bbogush/nand_programmer/qt/parallel_chip_db.h

/*  Copyright (C) 2020 NANDO authors
 *  This program is free software; you can redistribute it and/or modify
 *  it under the terms of the GNU General Public License version 3.
 */

#ifndef PARALLEL_CHIP_DB_H
#define PARALLEL_CHIP_DB_H

#include "chip_db.h"
#include "parallel_chip_info.h"

#include <cstdint>
#include <QString>
#include <QObject>
#include <QVector>
#include <QFile>

class ParallelChipDb : public ChipDb
{
private:
    QString dbFileName = "nando_parallel_chip_db.csv";

protected:
    QString getDbFileName() override;
    ChipInfo *stringToChipInfo(const QString &s) override;
    int chipInfoToString(ChipInfo *chipInfo, QString &s) override;

public:
    enum
    {
        CHIP_PARAM_NAME,
        CHIP_PARAM_PAGE_SIZE,
        CHIP_PARAM_BLOCK_SIZE,
        CHIP_PARAM_TOTAL_SIZE,
        CHIP_PARAM_SPARE_SIZE,
        CHIP_PARAM_BB_MARK_OFF,
        CHIP_PARAM_T_CS,
        CHIP_PARAM_T_CLS,
        CHIP_PARAM_T_ALS,
        CHIP_PARAM_T_CLR,
        CHIP_PARAM_T_AR,
        CHIP_PARAM_T_WP,
        CHIP_PARAM_T_RP,
        CHIP_PARAM_T_DS,
        CHIP_PARAM_T_CH,
        CHIP_PARAM_T_CLH,
        CHIP_PARAM_T_ALH,
        CHIP_PARAM_T_WC,
        CHIP_PARAM_T_RC,
        CHIP_PARAM_T_REA,
        CHIP_PARAM_ROW_CYCLES,
        CHIP_PARAM_COL_CYCLES,
        CHIP_PARAM_READ1_CMD,
        CHIP_PARAM_READ2_CMD,
        CHIP_PARAM_READ_SPARE_CMD,
        CHIP_PARAM_READ_ID_CMD,
        CHIP_PARAM_RESET_CMD,
        CHIP_PARAM_WRITE1_CMD,
        CHIP_PARAM_WRITE2_CMD,
        CHIP_PARAM_ERASE1_CMD,
        CHIP_PARAM_ERASE2_CMD,
        CHIP_PARAM_STATUS_CMD,
        CHIP_PARAM_SET_FEATURE_CMD,
        CHIP_PARAM_ENABLE_HW_ECC_ADDR,
        CHIP_PARAM_ENABLE_HW_ECC_VALUE,
        CHIP_PARAM_DISABLE_HW_ECC_VALUE,
        CHIP_PARAM_ID1,
        CHIP_PARAM_ID2,
        CHIP_PARAM_ID3,
        CHIP_PARAM_ID4,
        CHIP_PARAM_ID5,
        CHIP_PARAM_NUM,
    };

    explicit ParallelChipDb();
    virtual ~ParallelChipDb();

    int getIdByChipId(uint32_t id1, uint32_t id2, uint32_t id3, uint32_t id4,
        uint32_t id5);
    QString getNameByChipId(uint32_t id1, uint32_t id2,
        uint32_t id3, uint32_t id4, uint32_t id5) override;
    quint64 getChipParam(int chipIndex, int paramIndex);
    int setChipParam(int chipIndex, int paramIndex, quint64 paramValue);
};

#endif // PARALLEL_CHIP_DB_H
