bbogush/nand_programmer/qt/logger.cpp

/*  Copyright (C) 2020 NANDO authors
 *  This program is free software; you can redistribute it and/or modify
 *  it under the terms of the GNU General Public License version 3.
 */

#include "logger.h"
#include <QDebug>
#include <QScrollBar>
#include <QObject>

Q_DECLARE_METATYPE(QTextCursor)
Q_DECLARE_METATYPE(QtMsgType)

Logger *Logger::logger;
QTextEdit *Logger::logTextEdit;
int Logger::refCount;

void Logger::logHandler(QtMsgType type, const QMessageLogContext &context ,
    const QString &msg)
{
    const char *prefix = "";
    QString formatMsg;

    (void)context;

    switch (type) {
    case QtDebugMsg:
        prefix = "Debug: ";
        break;
    case QtInfoMsg:
        prefix = "Info: ";
        break;
    case QtWarningMsg:
        prefix = "Warning: ";
        break;
    case QtCriticalMsg:
        prefix = "Error: ";
        break;
    case QtFatalMsg:
        prefix = "Fatal error: ";
        break;
    }

    formatMsg = QString("%1%2\n").arg(prefix).arg(msg);

    if (type == QtFatalMsg || !logTextEdit)
    {
        QByteArray ba = formatMsg.toLatin1();
        fputs(ba.data(), stderr);
        if (type == QtFatalMsg)
            abort();
    }
    else
    {
        logTextEdit->moveCursor(QTextCursor::End);
        logTextEdit->insertPlainText(formatMsg);

        logTextEdit->verticalScrollBar()->
            setValue(logTextEdit->verticalScrollBar()->maximum());
    }
}

Logger::Logger()
{
    qRegisterMetaType<QTextCursor>();
    qRegisterMetaType<QtMsgType>();

    QObject::connect(this, SIGNAL(log(QString)), this, SLOT(slotLog(QString)));
    qInstallMessageHandler(logHandler);
    oldBuf = std::cerr.rdbuf();
    std::cerr.rdbuf(this);
}

Logger::~Logger()
{
    std::cerr.rdbuf(oldBuf);
    qInstallMessageHandler(nullptr);
}

Logger *Logger::getInstance()
{
    if (!logger)
        logger = new Logger();
    refCount++;

    return logger;
}

void Logger::putInstance()
{
    if (!refCount)
    {
        qWarning() << "Logger is released without being allocated";
        return;
    }

    if (!--refCount && logger)
    {
        delete logger;
        logger = nullptr;
        logTextEdit = nullptr;
    }
}

void Logger::setTextEdit(QTextEdit *textEdit)
{
    logTextEdit = textEdit;
}

std::basic_streambuf<char>::int_type Logger::overflow(int_type v)
{
    emit log(tempBuf);
    tempBuf.clear();

    return v;
}

std::streamsize Logger::xsputn(const char *p, std::streamsize n)
{
    tempBuf.append(QString::fromLatin1(p, n));

    return n;
}

void Logger::slotLog(QString msg)
{
    qCritical() << msg;
}
